mxtommy/SigkSens/hardware/WemosD1Mini/Kicad/SigKSens.kicad_pcb

## KiCad design Elektronic/rgbPanel/tt-display.sch

Schematic: tt-display.sch

Parts:
Hub75: ARDUINO_MEGA_SHIELD
SW1: Right
SW2: Left
SW3: Shift

Notes on the sheet:
D0-D8 for Wemos D1 mini
Oled and Hub75
TT Display with RGB Matrix
