mxtommy/SigkSens/SigkSens/src/services/signalK.cpp

#ifdef ESP8266
extern "C" {
#include "user_interface.h"
}
#endif
#include <ArduinoJson.h>     //https://github.com/bblanchon/ArduinoJson

#include "../../config.h"
#include "../../sigksens.h"
#include "../sensors/sensorStorage.h"

#include "signalK.h"

#include "../net/webSocket.h"

#ifdef ENABLE_DIGITALOUT
 #include "../sensors/digitalOut/digitalOut.h"
#endif


// forward declarations
void handleSignalK();


void setupSignalK() {
  app.onRepeat(SLOW_LOOP_DELAY, handleSignalK);
}


void handleSignalK() {
  bool needToSend = false;
  
  sensorStorageForEach([&](SensorInfo* si) {
    if (si->isUpdated) {
      for (int x=0;x<MAX_SENSOR_ATTRIBUTES; x++) { // check if any paths are set.
        if (strcmp(si->attrName[x].c_str(), "") == 0) {
          break; // if attr is empty, no more attr's for this sensor
        } 
        if (strcmp(si->signalKPath[x].c_str(),  "") != 0) {
           needToSend = true;
        }      
      }
      
    }
  });
  if (needToSend) {
    sendDelta();
  }
}


void receiveDelta(uint8_t * payload) {
  DynamicJsonBuffer jsonBuffer;
  char tempStr[255];
  bool tempBool;

  JsonObject& root = jsonBuffer.parseObject(payload);
  if (!root.success()) {
    Serial.println(F("parseObject() failed"));
    return;
  }
  //root.prettyPrintTo(Serial);

  if (root.containsKey("put")) {
    for (uint8_t i=0; i < root["put"].size(); i++) {
      strcpy(tempStr, root["put"][i]["path"]);
      sensorStorage[(int)SensorType::digitalOut].forEach([&](SensorInfo* si) {
        if (strcmp(si->signalKPath[0].c_str(), tempStr) == 0) {
           //Serial.println(si->address);
           //Serial.println(si->signalKPath[0]);

          if (root["put"][i]["value"].is<bool>()) {
            tempBool = root["put"][i]["value"];
#ifdef ENABLE_DIGITALOUT
            digitalOutSetBooleanValue(si->address, tempBool);
#endif
          }
        }
      });

      
    }
  }
  



}


void sendDelta() {
  bool needToSend = false;

  String deltaText;

  DynamicJsonBuffer jsonBuffer; 

  //  build delta message
  JsonObject& delta = jsonBuffer.createObject();

  //updated array
  JsonArray& updatesArr = delta.createNestedArray("updates");
  
  sensorStorageForEach([&](SensorInfo* si) {
    if (si->isUpdated) {
      needToSend = false;
      //make sure we have paths set for this sensor
      for (int x=0;x<MAX_SENSOR_ATTRIBUTES; x++) { // check if any paths are set.
        if (strcmp(si->attrName[x].c_str(), "") == 0) {
          break; // if attr is empty, no more attr's for this sensor
        } 
        if (strcmp(si->signalKPath[x].c_str(),  "") != 0) {
           needToSend = true;
        }      
      }
      if (needToSend) {
        JsonObject& thisUpdate = updatesArr.createNestedObject();

        JsonObject& source = thisUpdate.createNestedObject("source");
        source["label"] = myHostname;
        source["src"] = si->address;
        // values array
      
        JsonArray& values = thisUpdate.createNestedArray("values");

        for (int x=0;x<MAX_SENSOR_ATTRIBUTES; x++) {
          if (strcmp(si->attrName[x].c_str(), "") == 0) {
            break; // if attr is empty, no more attr's for this sensor
          } 
          if (strcmp(si->signalKPath[x].c_str(),  "") == 0) {
            continue; // no path set for this...
          }
          JsonObject& thisValue = values.createNestedObject();
          thisValue["path"] = si->signalKPath[x].c_str();
          thisValue["value"] = RawJson(si->valueJson[x].c_str());
        }
      }
      //reset updated
      si->isUpdated = false;
    }
  });

  delta.printTo(deltaText);

  #ifdef ENABLE_SERIAL_DELTA
  Serial.println(deltaText);
  #endif
  
  #ifdef ENABLE_WEBSOCKET_SERVER
  webSocketServer.broadcastTXT(deltaText);
  #endif
  
  if (signalKClientInfo.connected) { // client
    signalKClientInfo.client.sendTXT(deltaText);
    ledBlinker.flip();
  }
  
}
