mxtommy/SigkSens/SigkSens/src/net/ota.cpp

#include "ota.h"

#include "../../config.h"
#include "../../sigksens.h"

#include <ArduinoOTA.h>


void handleOTA() {
  ArduinoOTA.handle();
}

void setupOTA() {
#ifdef OTA_PASSWORD
  ArduinoOTA.setPassword((const char *)OTA_PASSWORD);
#endif
  ArduinoOTA.onStart([]() {
    Serial.println("Starting OTA");
  });
  ArduinoOTA.onEnd([]() {
    Serial.println("\nEnd");
  });
  ArduinoOTA.onProgress([](unsigned int progress, unsigned int total) {
    Serial.printf("Progress: %u%%\r", (progress / (total / 100)));
  });
  ArduinoOTA.onError([](ota_error_t error) {
    Serial.printf("Error[%u]: ", error);
    if (error == OTA_AUTH_ERROR) Serial.println("Auth Failed");
    else if (error == OTA_BEGIN_ERROR) Serial.println("Begin Failed");
    else if (error == OTA_CONNECT_ERROR) Serial.println("Connect Failed");
    else if (error == OTA_RECEIVE_ERROR) Serial.println("Receive Failed");
    else if (error == OTA_END_ERROR) Serial.println("End Failed");
  });
  ArduinoOTA.begin();
  //app.onTick(&handleOTA);
  app.onRepeat(20, handleOTA);
}
