mxtommy/SigkSens/analogIn.h

#ifndef _analogin_H_
#define _analogin_H_

extern "C" {
#include "user_interface.h"
}

#ifdef ENABLE_ANALOGIN
bool getSensorAnalogInPresent();
#endif

class AinSensorInfo : public SensorInfo {
  public:
    AinSensorInfo(String addr);
    AinSensorInfo( String addr, 
                   String path0, 
                   float offset0,
                   float scale0);
    static AinSensorInfo *fromJson(JsonObject &jsonSens);
    void toJson(JsonObject &jsonSens);

};

void setupAnalogIn(bool&);
void handleAnalogIn(bool&);
void interruptReadADC(void *pArg);
void readADC();
void updateAnalogIn();


#endif
